Technofrikus/QASS/QASS Case/variable layer height.png

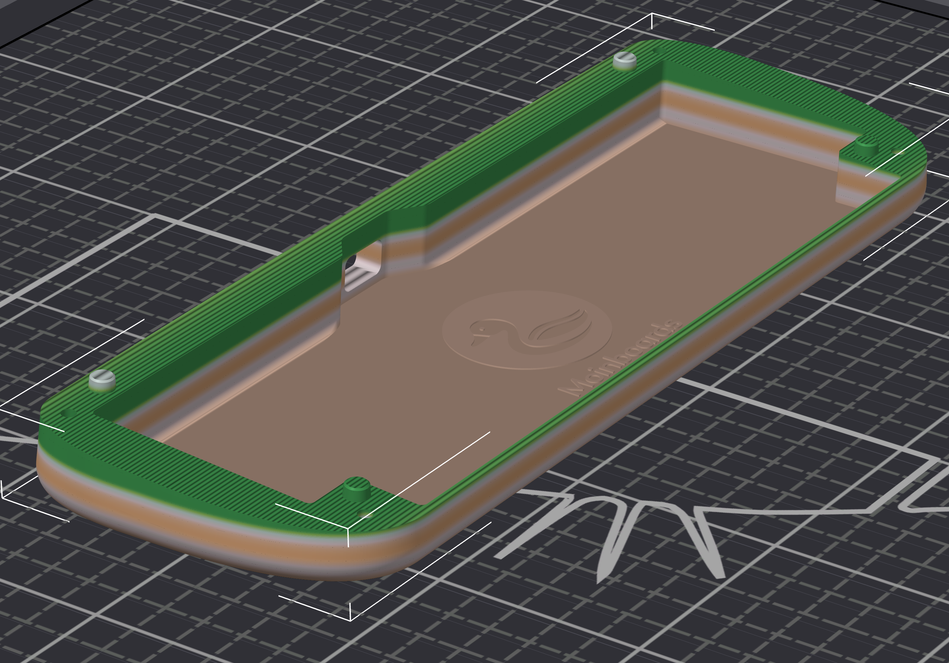
QASS Case/variable layer height.png
