Technofrikus/QASS/QASS_2024-Mar-04_06-24-00PM-000_CustomizedView11273287100.png

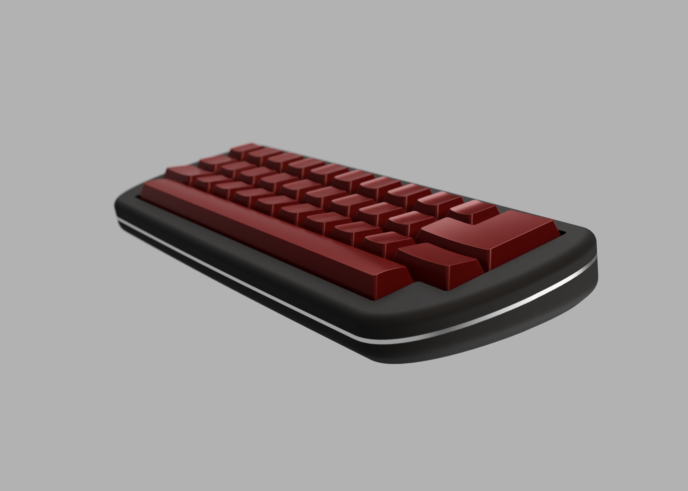
QASS_2024-Mar-04_06-24-00PM-000_CustomizedView11273287100.png
