Technofrikus/QASS/QASS_2024-Mar-04_06-30-16PM-000_CustomizedView29996760384.png

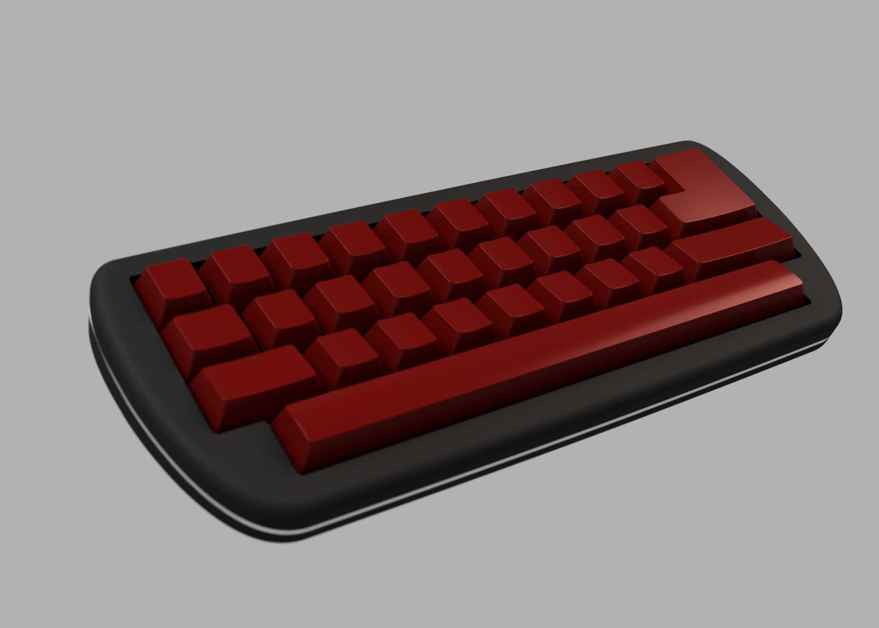
QASS_2024-Mar-04_06-30-16PM-000_CustomizedView29996760384.png
