Technofrikus/QASS/QASS_2024-Mar-04_06-31-55PM-000_CustomizedView32080402474.png

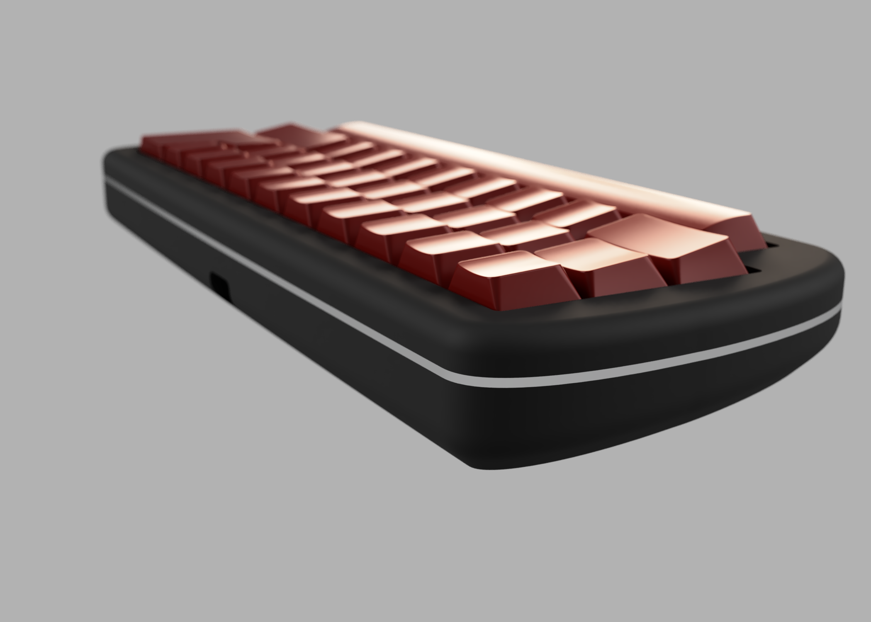
QASS_2024-Mar-04_06-31-55PM-000_CustomizedView32080402474.png
