Technofrikus/QASS/QASS_2024-Mar-04_06-41-01PM-000_CustomizedView6309640334.png

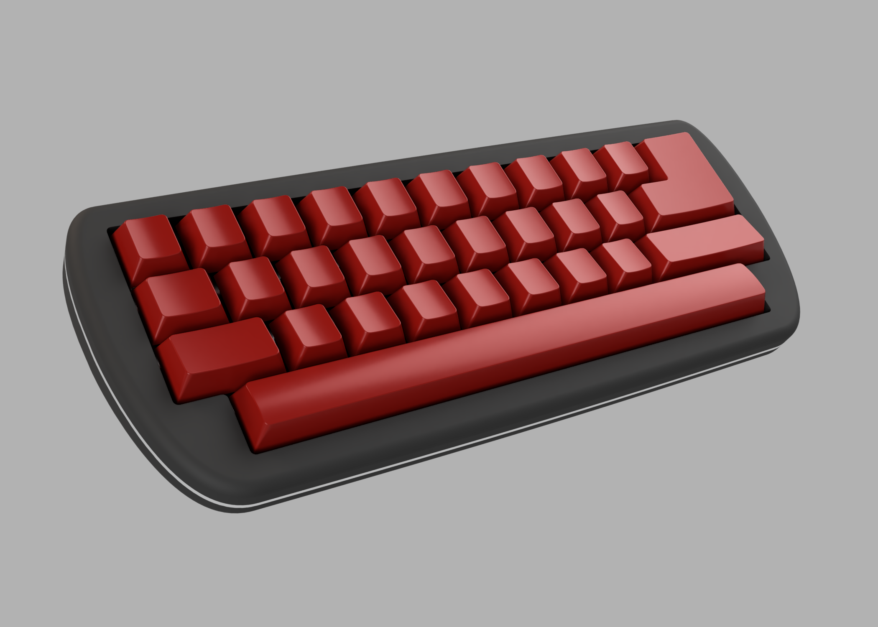
QASS_2024-Mar-04_06-41-01PM-000_CustomizedView6309640334.png
