Technofrikus/QASS/QASS_2024-Mar-04_06-41-19PM-000_CustomizedView46184224152.png

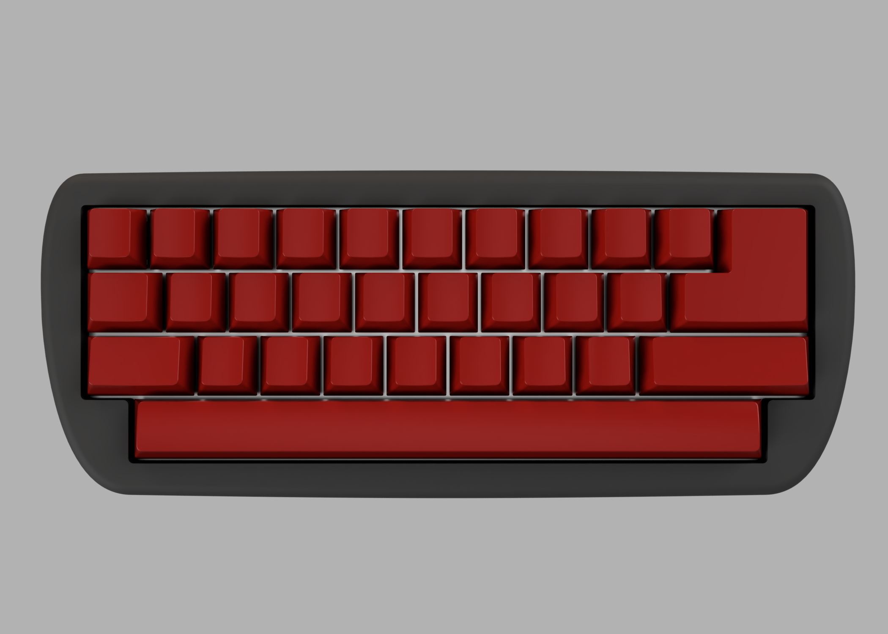
QASS_2024-Mar-04_06-41-19PM-000_CustomizedView46184224152.png
