Technofrikus/QASS/QASS_2024-Mar-05_09-21-43PM-000_CustomizedView12471374338.png

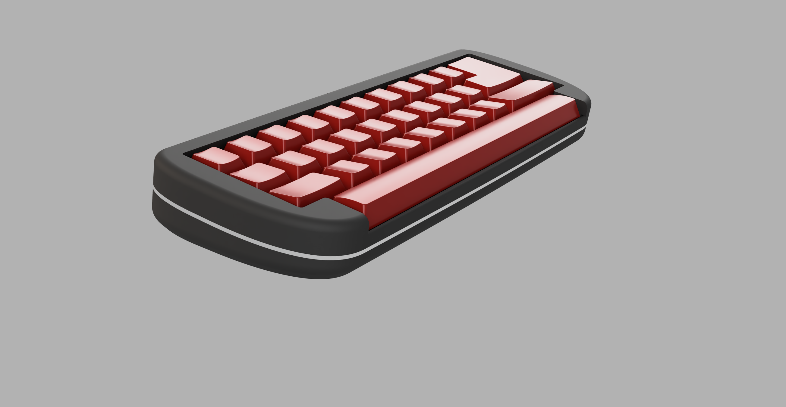
QASS_2024-Mar-05_09-21-43PM-000_CustomizedView12471374338.png
