Technofrikus/QASS/QASS_2024-Mar-06_03-33-23PM-000_CustomizedView4689084506.png

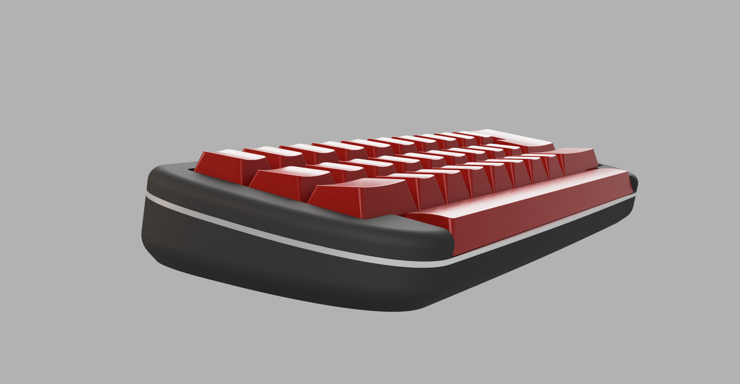
QASS_2024-Mar-06_03-33-23PM-000_CustomizedView4689084506.png
