Technofrikus/QASS/QASS_2024-Mar-06_03-36-36PM-000_CustomizedView24366457529.png

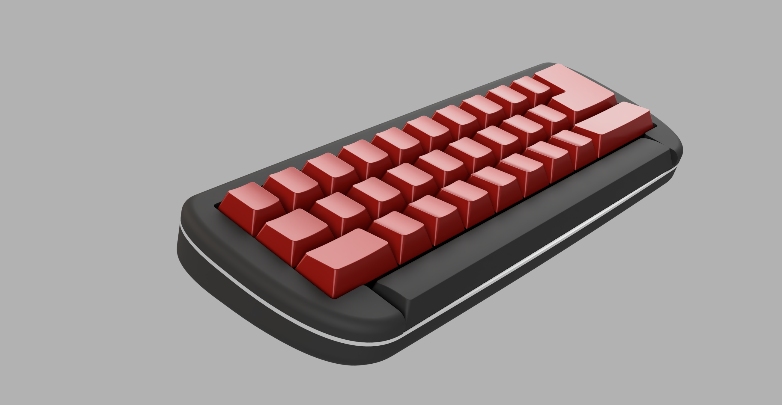
QASS_2024-Mar-06_03-36-36PM-000_CustomizedView24366457529.png
