Technofrikus/QASS/QASS_PCB/QASS_PCB_B.jpeg

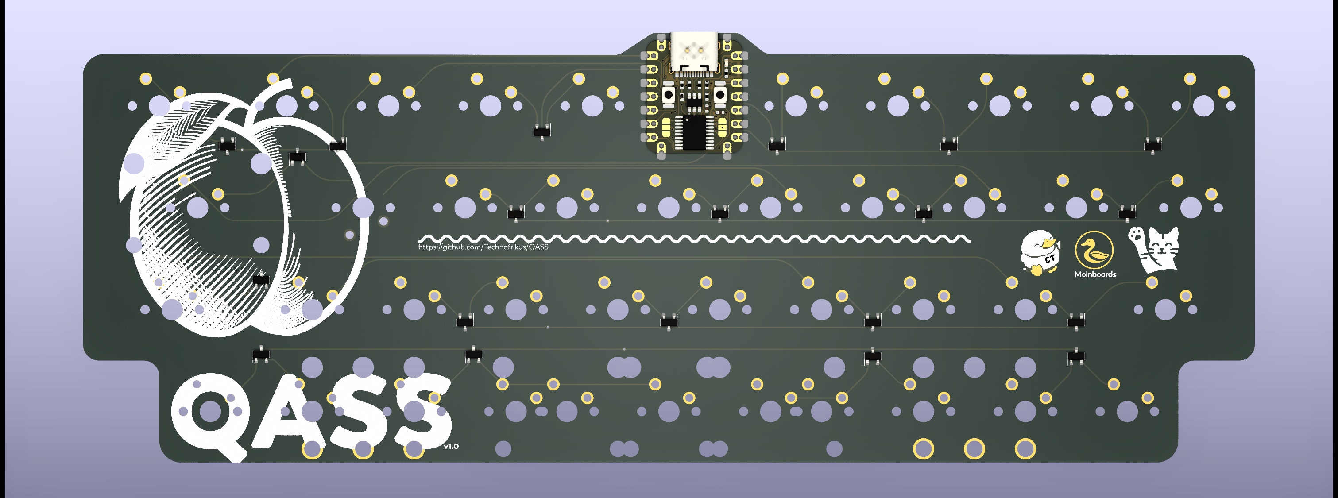
QASS_PCB/QASS_PCB_B.jpeg
