Technofrikus/QASS/QASS_PCB/QASS_PCB_B.png

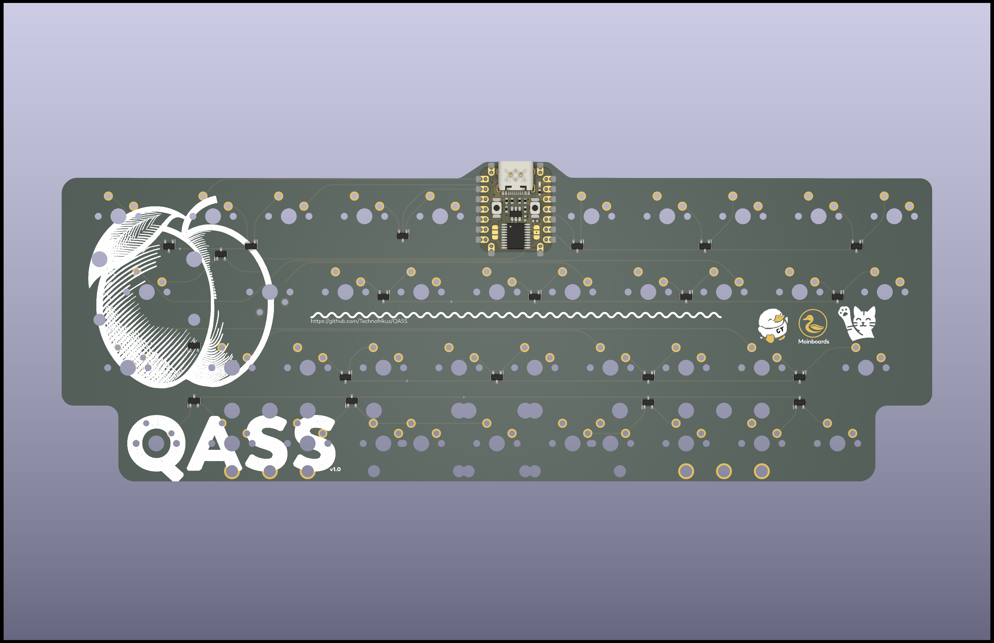
QASS_PCB/QASS_PCB_B.png
