Technofrikus/QASS/QASS_PCB/QASS_PCB_F.jpeg

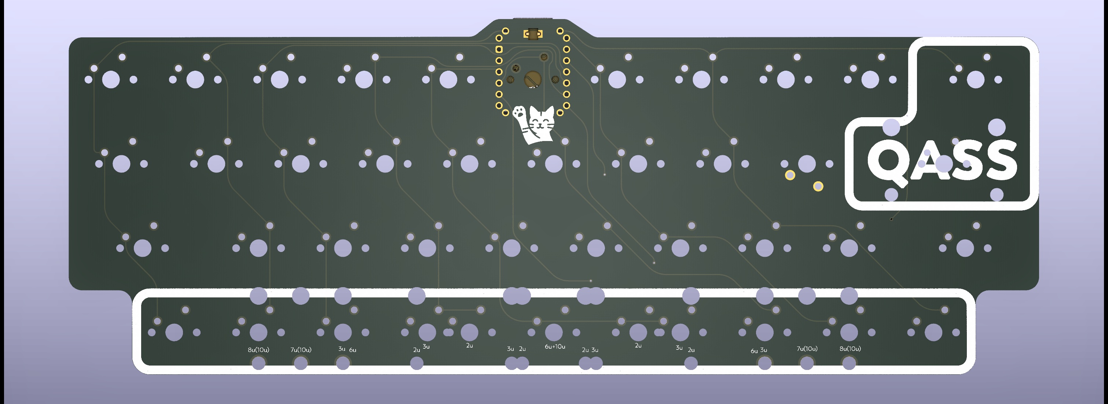
QASS_PCB/QASS_PCB_F.jpeg
