Technofrikus/QASS/QASS_PCB/QASS_PCB_F.png

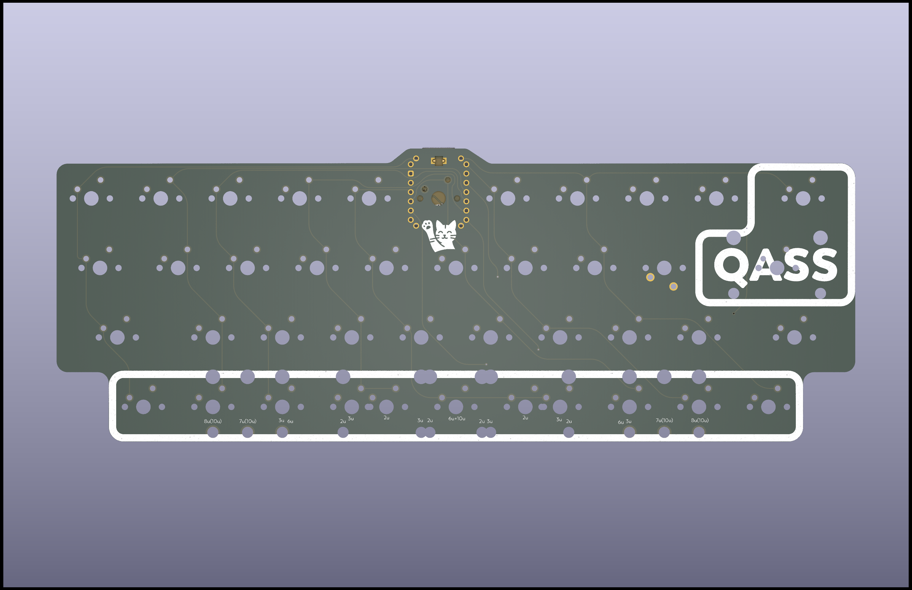
QASS_PCB/QASS_PCB_F.png
